SamWibatt/FPGA_AI_SRAM/blinky.v

// this will be a module to access a 1Mx8 SRAM / flash module such as I own for soldering practice. They will be useful for
// testing data structure acceleration, too, I reckon.

`default_nettype none

// FOR STARTERS JUST USING DAN GISSELQUIST'S BLINKY
module blinky(
    input wire i_clk,
    output wire o_led       //temp debug
    //here will go all the address and data lines and stuff - make the addr width variable
    );

    parameter CBITS = 25;

    //here will go all the address and data lines and stuff

    reg	[CBITS-1:0]	counter = 0;
    always @(posedge i_clk)
    counter <= counter + 1'b1;
    assign o_led = counter[CBITS-1];
endmodule
